Tinkerforge/piezo-speaker-bricklet/software/src/piezo-speaker.h

/* piezo-speaker-bricklet
 * Copyright (C) 2013 Olaf Lüke <olaf@tinkerforge.com>
 *
 * piezo-speaker.h: Implementation of Piezo Speaker Bricklet messages
 *
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
 * You should have received a copy of the GNU Lesser General Public
 * License along with this library; if not, write to the
 * Free Software Foundation, Inc., 59 Temple Place - Suite 330,
 * Boston, MA 02111-1307, USA.
 */

#ifndef PIEZO_BUZZER_H
#define PIEZO_BUZZER_H

#include <stdint.h>

#include "bricklib/com/com_common.h"

#define EEPROM_CALIBRATION_POSITION (I2C_EEPROM_INTERNAL_ADDRESS_PLUGIN + \
                                     BRICKLET_PLUGIN_MAX_SIZE)
#define EEPROM_CALIBRATION_LENGTH   CALIBRATION_LENGTH

#define FEEDBACK_TICK_MAX 63999

#define FREQUENCY_VALUE_SUM_MAX 512
#define FREQUENCY_VALUE_MAX 256

#define FREQUENCY_MIN 585
#define FREQUENCY_MAX 7100

#define I2C_EEPROM_ADDRESS_HIGH 84

#define I2C_ADDRESS_HIGH 47 // 0b0101111
#define I2C_ADDRESS_LOW 46 //  0b0101110
#define I2C_INTERNAL_ADDRESS_TEMPERATURE 0x0
#define I2C_INTERNAL_ADDRESS_BYTES 1
#define I2C_DATA_LENGTH 2

#define I2C_COMMAND_WIPER0 (0 << 4)
#define I2C_COMMAND_WIPER1 (1 << 4)
#define I2C_ACTION_WRITE   (0 << 2)
#define I2C_ACTION_INCR    (1 << 2)
#define I2C_ACTION_DECR    (2 << 2)
#define I2C_ACTION_READ    (3 << 2)

#define FID_BEEP 1
#define FID_MORSE_CODE 2
#define FID_CALIBRATE 3
#define FID_BEEP_FINISHED 4
#define FID_MORSE_CODE_FINISHED 5

typedef struct {
	MessageHeader header;
} __attribute__((__packed__)) StandardMessage;

typedef struct {
	MessageHeader header;
	uint32_t duration;
	uint16_t frequency;
} __attribute__((__packed__)) Beep;

typedef struct {
	MessageHeader header;
	char morse[60];
	uint16_t frequency;
} __attribute__((__packed__)) MorseCode;

typedef struct {
	MessageHeader header;
} __attribute__((__packed__)) Calibrate;

typedef struct {
	MessageHeader header;
	bool calibration;
} __attribute__((__packed__)) CalibrateReturn;

uint8_t get_i2c_address(void);
void set_frequency(uint16_t frequency);
void beep(const ComType com, const Beep *data);
void morse_code(const ComType com, const MorseCode *data);
void calibrate(const ComType com, const Calibrate *data);

void load_calibration(void);
void save_calibration(void);

void invocation(const ComType com, const uint8_t *data);
void constructor(void);
void destructor(void);
void tick(const uint8_t tick_type);

#endif
